ki-manufaktur/neurodots/doc/1.jpg

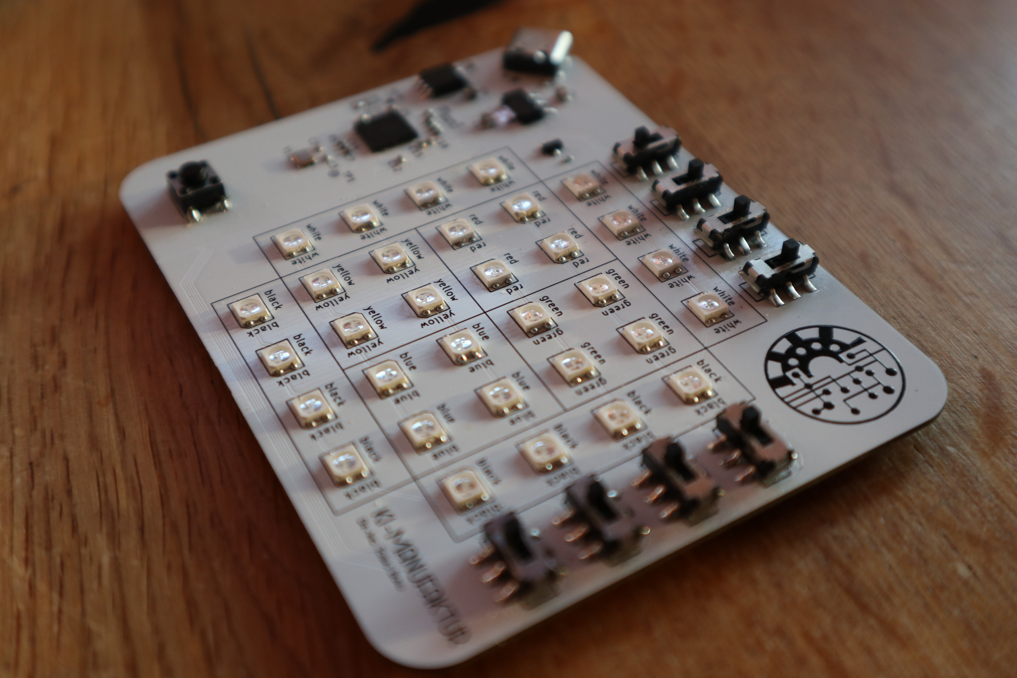
doc/1.jpg
