ki-manufaktur/neurodots/doc/2.jpg

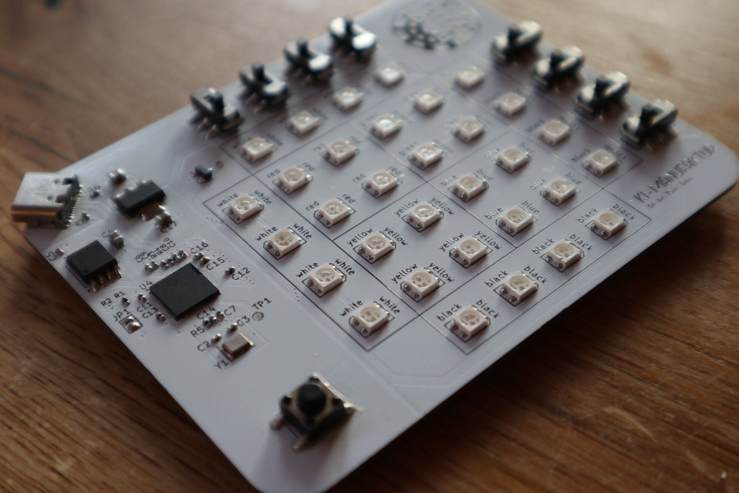
doc/2.jpg
