ki-manufaktur/neurodots/doc/4.jpg

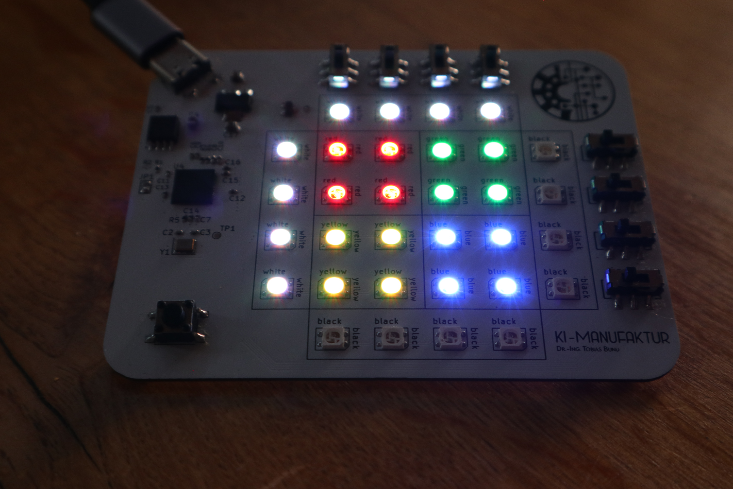
doc/4.jpg
